javeharron/magnetarAlpha/Magnetar-Photos/Magnetar-MCUFC.png

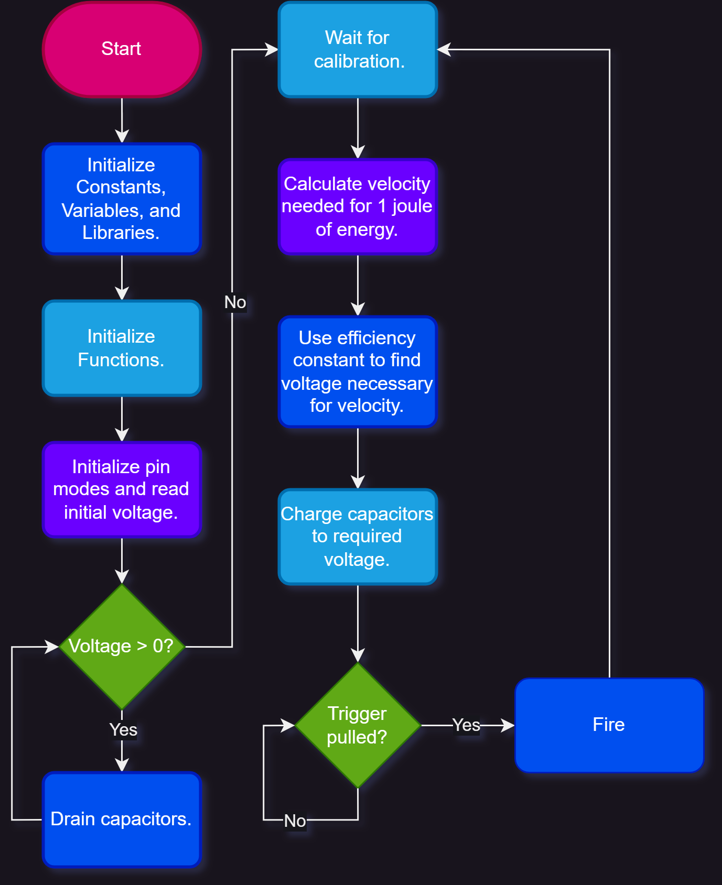
Magnetar-Photos/Magnetar-MCUFC.png
